mandraga/FE1.1S_USBHUB-M200fork/Usb_Hub_Pictures/1.jpg

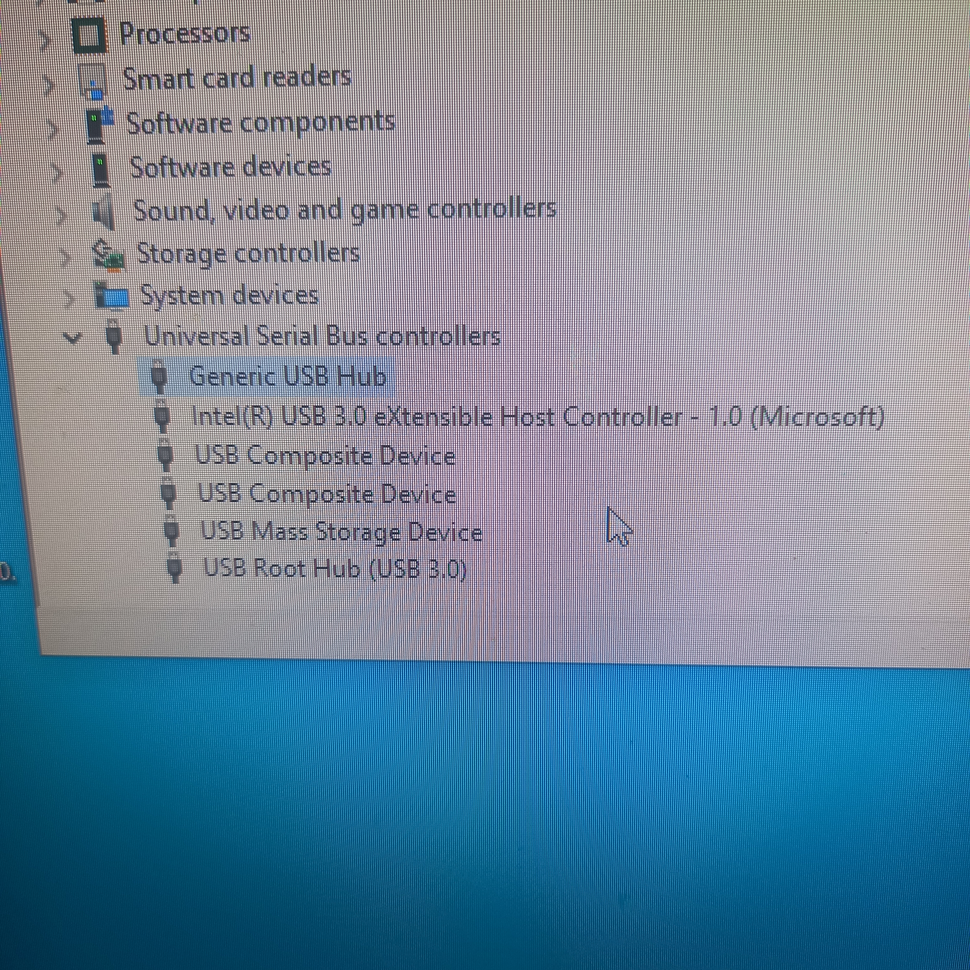
Usb_Hub_Pictures/1.jpg
